michalin/ZX2020/Schematic/TMS9918-2.kicad_sch

## KiCad design Schematic/TMS9918-2.kicad_sch (2022-06-24)

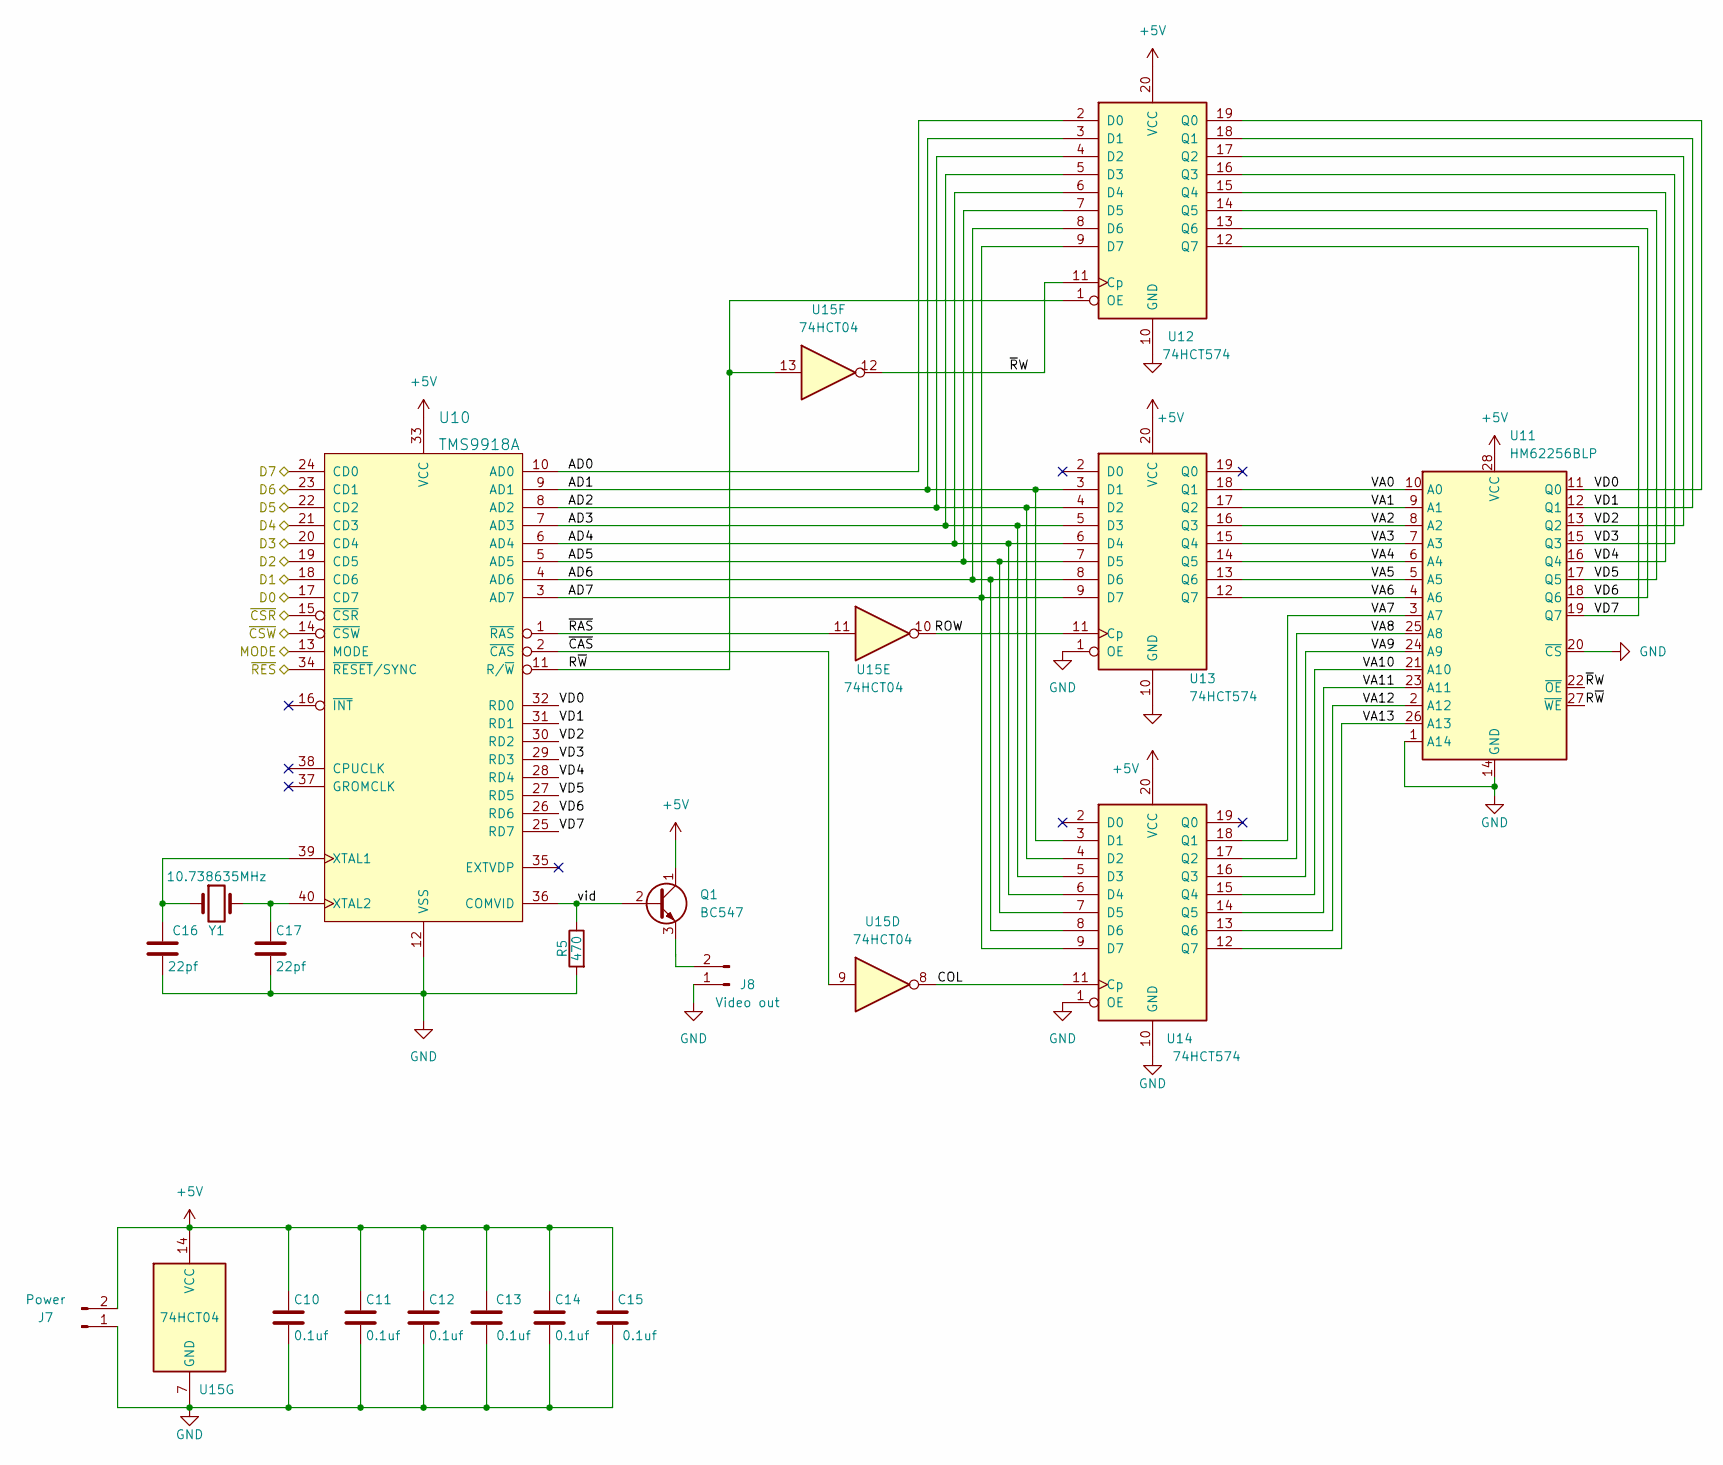
[picture p3: schematic TMS9918-2.kicad_sch]

Parts:
C10, C11, C12, C13, C14, C15: 0.1uf; C_Disc_D3.0mm_W1.6mm_P2.50mm
C16, C17: 22pf; C_Disc_D3.0mm_W1.6mm_P2.50mm
J7: Power; PinHeader_1x02_P2.54mm_Vertical
J8: Video out; PinHeader_1x02_P2.54mm_Horizontal
Q1: BC547; TO-92_Inline
R5: 470; R_Axial_DIN0207_L6.3mm_D2.5mm_P7.62mm_Horizontal
U10: TMS9918A; DIP-40_W15.24mm
U11: HM62256BLP; DIP-28_W15.24mm
U12, U13, U14: 74HCT574; DIP-20_W7.62mm_Socket
U15: 74HCT04; DIP-14_W7.62mm_Socket
Y1: 10.738635MHz; Crystal_HC49-4H_Vertical

Connections:
+5V: C10.1, C11.1, C12.1, C13.2, C14.1, C15.1, J7.2, Q1.1 (C), U10.33 (VCC), U11.28 (VCC), U12.20 (VCC), U13.20 (VCC), U14.20 (VCC), U15.14 (VCC)
AD0: U10.10 (AD0), U12.2 (D0)
AD1: U10.9 (AD1), U12.3 (D1), U13.3 (D1), U14.3 (D1)
AD2: U10.8 (AD2), U12.4 (D2), U13.4 (D2), U14.4 (D2)
AD3: U10.7 (AD3), U12.5 (D3), U13.5 (D3), U14.5 (D3)
AD4: U10.6 (AD4), U12.6 (D4), U13.6 (D4), U14.6 (D4)
AD5: U10.5 (AD5), U12.7 (D5), U13.7 (D5), U14.7 (D5)
AD6: U10.4 (AD6), U12.8 (D6), U13.8 (D6), U14.8 (D6)
AD7: U10.3 (AD7), U12.9 (D7), U13.9 (D7), U14.9 (D7)
COL: U14.11 (Cp), U15.8
D0: U10.17 (CD7)
D1: U10.18 (CD6)
D2: U10.19 (CD5)
D3: U10.20 (CD4)
D4: U10.21 (CD3)
D5: U10.22 (CD2)
D6: U10.23 (CD1)
D7: U10.24 (CD0)
GND: C10.2, C11.2, C12.2, C13.1, C14.2, C15.2, C16.2, C17.2, J7.1, J8.1, R5.2, U10.12 (VSS), U11.1 (A14), U11.14 (GND), U11.20 (~CS), U12.10 (GND), U13.1 (OE), U13.10 (GND), U14.1 (OE), U14.10 (GND), U15.7 (GND)
MODE: U10.13 (MODE)
unnamed: C16.1, U10.39 (XTAL1), Y1.1
unnamed: C17.1, U10.40 (XTAL2), Y1.2
unnamed: J8.2, Q1.3 (E)
ROW: U13.11 (Cp), U15.10
R~W: U10.11 (R/~W), U11.27 (~WE), U12.1 (OE), U15.13
VA0: U11.10 (A0), U13.18 (Q1)
VA1: U11.9 (A1), U13.17 (Q2)
VA2: U11.8 (A2), U13.16 (Q3)
VA3: U11.7 (A3), U13.15 (Q4)
VA4: U11.6 (A4), U13.14 (Q5)
VA5: U11.5 (A5), U13.13 (Q6)
VA6: U11.4 (A6), U13.12 (Q7)
VA7: U11.3 (A7), U14.18 (Q1)
VA8: U11.25 (A8), U14.17 (Q2)
VA9: U11.24 (A9), U14.16 (Q3)
VA10: U11.21 (A10), U14.15 (Q4)
VA11: U11.23 (A11), U14.14 (Q5)
VA12: U11.2 (A12), U14.13 (Q6)
VA13: U11.26 (A13), U14.12 (Q7)
VD0: U10.32 (RD0), U11.11 (Q0), U12.19 (Q0)
VD1: U10.31 (RD1), U11.12 (Q1), U12.18 (Q1)
VD2: U10.30 (RD2), U11.13 (Q2), U12.17 (Q2)
VD3: U10.29 (RD3), U11.15 (Q3), U12.16 (Q3)
VD4: U10.28 (RD4), U11.16 (Q4), U12.15 (Q4)
VD5: U10.27 (RD5), U11.17 (Q5), U12.14 (Q5)
VD6: U10.26 (RD6), U11.18 (Q6), U12.13 (Q6)
VD7: U10.25 (RD7), U11.19 (Q7), U12.12 (Q7)
vid: Q1.2 (B), R5.1, U10.36 (COMVID)
~CAS: U10.2 (~CAS), U15.9
~CSR: U10.15 (~CSR)
~CSW: U10.14 (~CSW)
~RAS: U10.1 (~RAS), U15.11
~RES: U10.34 (~RESET/SYNC)
~RW: U11.22 (~OE), U12.11 (Cp), U15.12
