michalin/ZX2020/Schematic/zx2020.kicad_sch

## KiCad design Schematic/zx2020.kicad_sch (2022-06-24)

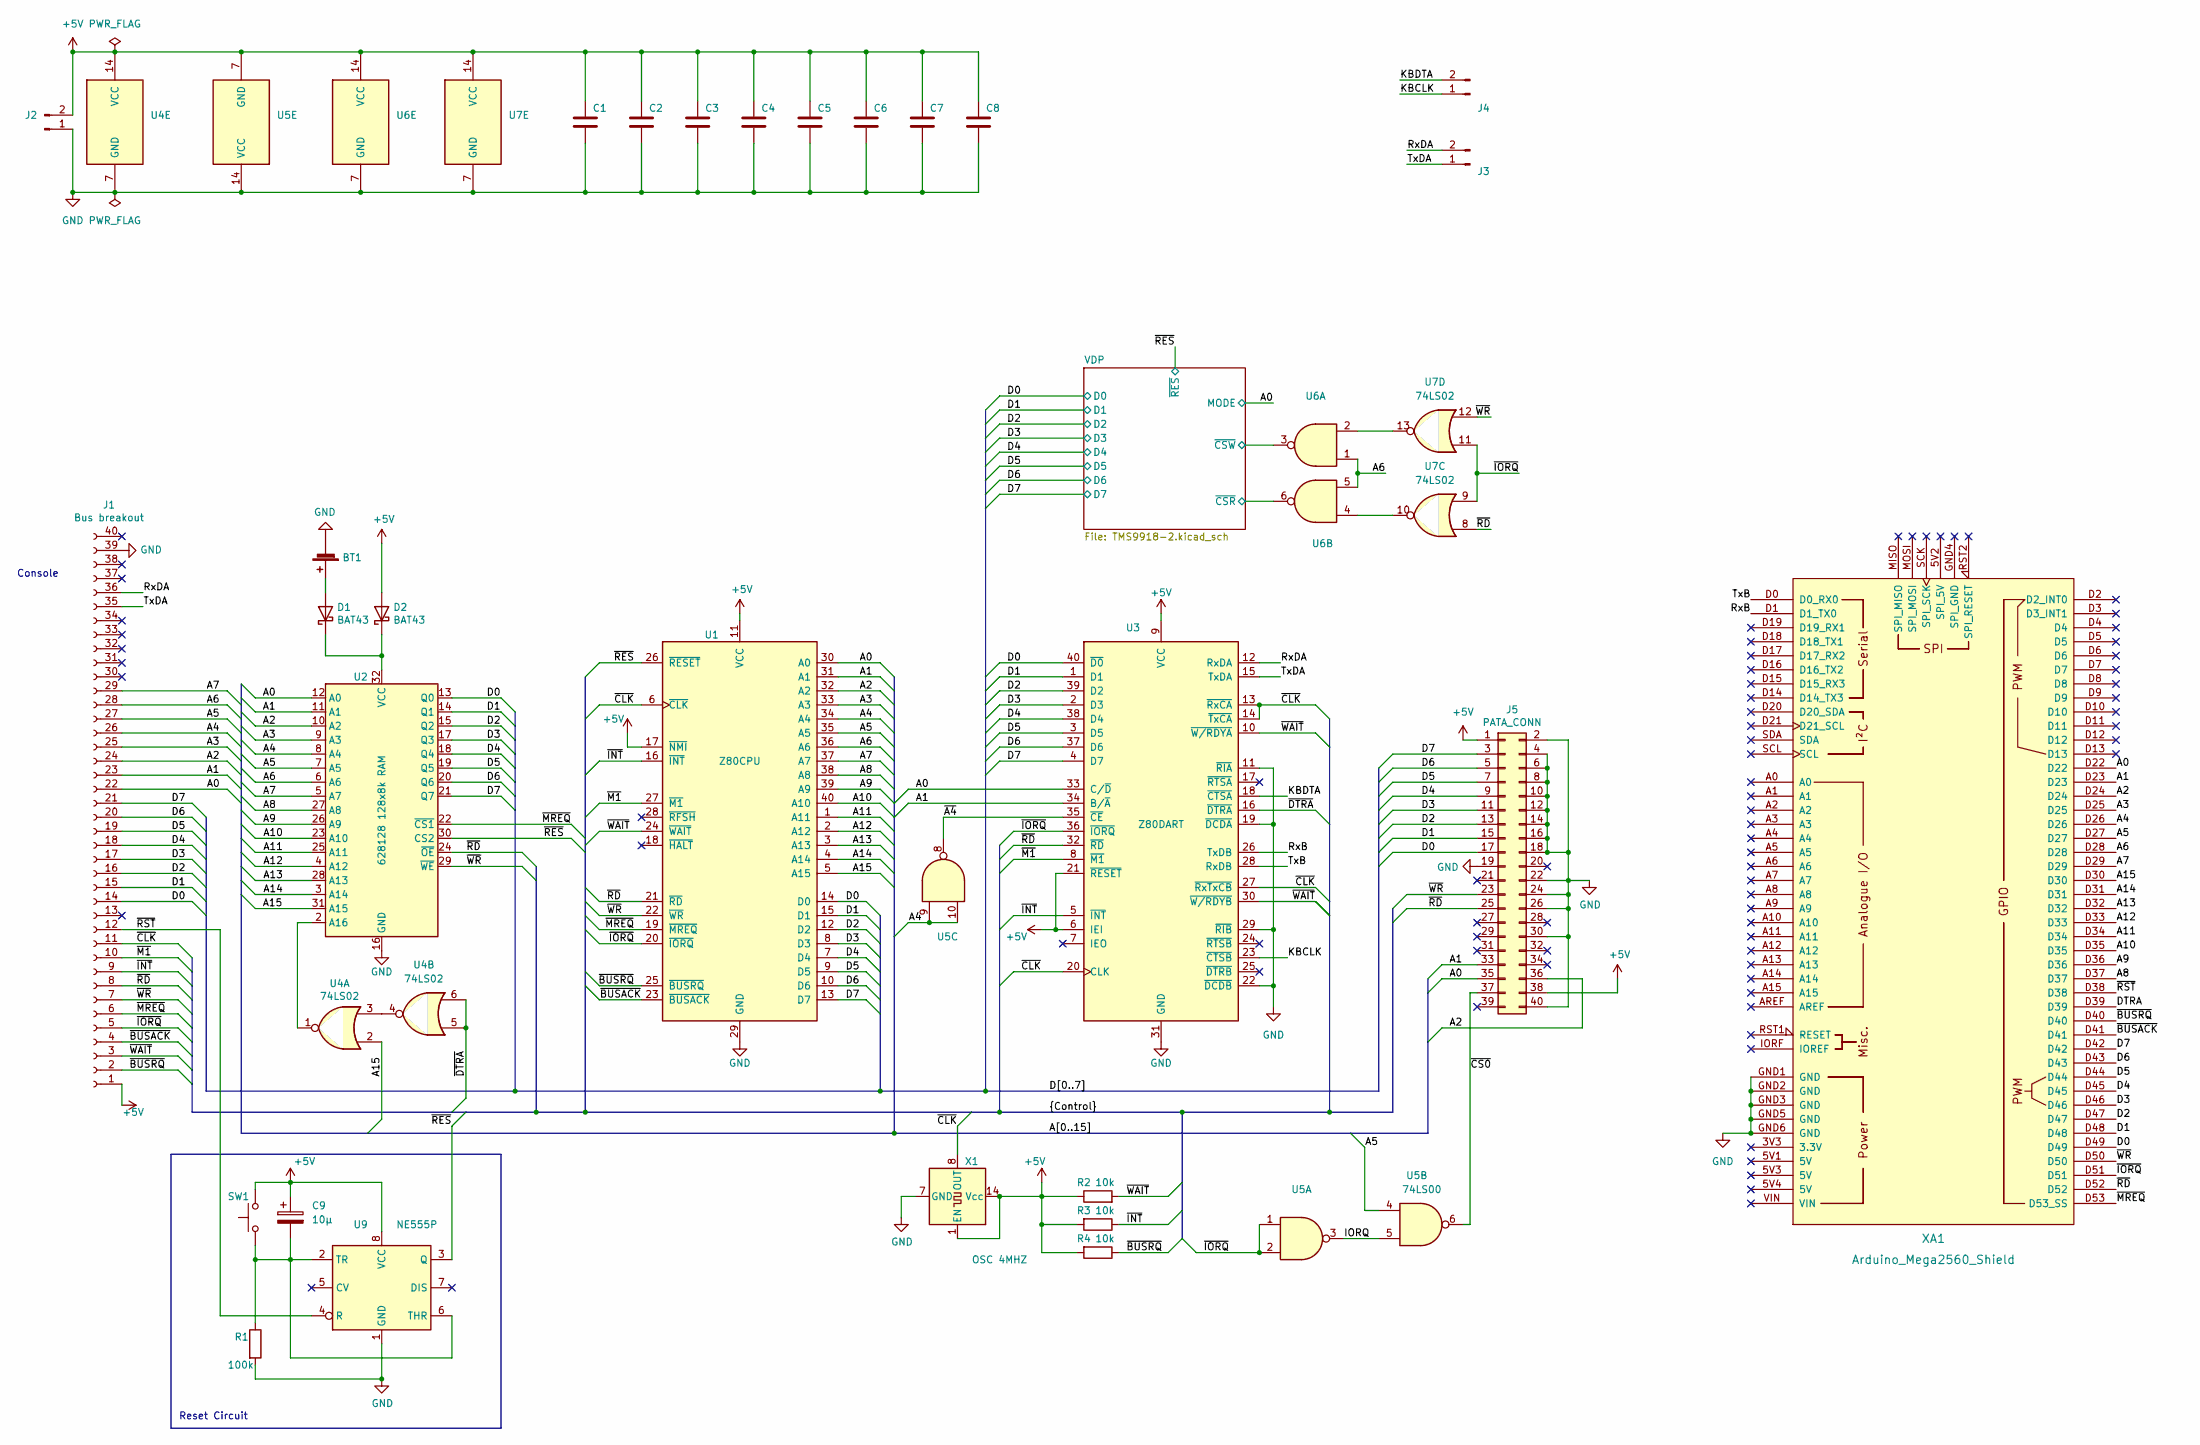
[picture p4: schematic zx2020.kicad_sch]

Parts:
BT1: Battery_Cell
C1, C2, C3, C4, C5, C6, C7, C8: (no value)
C9: 10µ
D1, D2: BAT43; D_DO-35_SOD27_P7.62mm_Horizontal
J1: Bus breakout; PinHeader_1x39_P2.54mm_Vertical
J2, J3, J4: (no value)
J5: PATA_CONN; PinHeader_2x20_P2.54mm_Horizontal
R1: 100k
R2, R3, R4: 10k
SW1: (no value)
U1: Z80CPU; DIP-40_W15.24mm
U2: 628128 128x8k RAM; DIP-32_W15.24mm
U3: Z80DART; DIP-40_W15.24mm
U4: 74LS02; DIP-14_W7.62mm
U5: 74LS00
U6, U7: (no value)
U9: NE555P; DIP-8_W7.62mm
X1: OSC 4MHZ; Oscillator_DIP-14
XA1: Arduino_Mega2560_Shield

Connections:
+5V: C1.1, C2.1, C3.1, C4.1, C5.1, C6.1, C7.1, C8.1, C9.1, D2.2 (A), J1.1, J2.2, J5.1, J5.38, R2.1, R3.2, R4.2, SW1.2, U1.11 (VCC), U1.17 (~NMI), U3.6 (IEI), U3.9 (VCC), U3.21 (~RESET), U4.14 (VCC), U5.7 (GND), U6.14 (VCC), U7.14 (VCC), U9.8 (VCC), X1.1 (EN), X1.14 (Vcc)
A0: J1.22, J5.35, U1.30 (A0), U2.12 (A0), U3.33 (C/~D), XA1.D22
A1: J1.23, J5.33, U1.31 (A1), U2.11 (A1), U3.34 (B/~A), XA1.D23
A2: J1.24, J5.36, U1.32 (A2), U2.10 (A2), XA1.D24
A3: J1.25, U1.33 (A3), U2.9 (A3), XA1.D25
A4: J1.26, U1.34 (A4), U2.8 (A4), U5.9, U5.10, XA1.D26
A5: J1.27, U1.35 (A5), U2.7 (A5), U5.4, XA1.D27
A6: J1.28, U1.36 (A6), U2.6 (A6), U6.1, U6.5, XA1.D28
A7: J1.29, U1.37 (A7), U2.5 (A7), XA1.D29
A8: U1.38 (A8), U2.27 (A8), XA1.D37
A9: U1.39 (A9), U2.26 (A9), XA1.D36
A10: U1.40 (A10), U2.23 (A10), XA1.D35
A11: U1.1 (A11), U2.25 (A11), XA1.D34
A12: U1.2 (A12), U2.4 (A12), XA1.D33
A13: U1.3 (A13), U2.28 (A13), XA1.D32
A14: U1.4 (A14), U2.3 (A14), XA1.D31
A15: U1.5 (A15), U2.31 (A15), U4.2, XA1.D30
D0: J1.14, J5.17, U1.14 (D0), U2.13 (Q0), U3.40 (~D0), XA1.D49
D1: J1.15, J5.15, U1.15 (D1), U2.14 (Q1), U3.1 (D1), XA1.D48
D2: J1.16, J5.13, U1.12 (D2), U2.15 (Q2), U3.39 (D2), XA1.D47
D3: J1.17, J5.11, U1.8 (D3), U2.17 (Q3), U3.2 (D3), XA1.D46
D4: J1.18, J5.9, U1.7 (D4), U2.18 (Q4), U3.38 (D4), XA1.D45
D5: J1.19, J5.7, U1.9 (D5), U2.19 (Q5), U3.3 (D5), XA1.D44
D6: J1.20, J5.5, U1.10 (D6), U2.20 (Q6), U3.37 (D6), XA1.D43
D7: J1.21, J5.3, U1.13 (D7), U2.21 (Q7), U3.4 (D7), XA1.D42
DTRA: XA1.D39
GND: BT1.2 (-), C1.2, C2.2, C3.2, C4.2, C5.2, C6.2, C7.2, C8.2, J1.39, J2.1, J5.2, J5.4, J5.6, J5.8, J5.10, J5.12, J5.14, J5.16, J5.18, J5.19, J5.22, J5.24, J5.26, J5.30, J5.40, R1.2, U1.29 (GND), U2.16 (GND), U3.11 (~RIA), U3.19 (~DCDA), U3.22 (~DCDB), U3.29 (~RIB), U3.31 (GND), U4.7 (GND), U5.14 (VCC), U6.7 (GND), U7.7 (GND), U9.1 (GND), X1.7 (GND), XA1.GND1 (GND), XA1.GND2 (GND), XA1.GND3 (GND), XA1.GND5 (GND), XA1.GND6 (GND)
IORQ: U5.3, U5.5
KBCLK: J4.1, U3.23 (~CTSB)
KBDTA: J4.2, U3.18 (~CTSA)
unnamed: BT1.1 (+), D1.2 (A)
unnamed: C9.2, R1.1, SW1.1, U9.2 (TR), U9.6 (THR)
unnamed: D1.1 (K), D2.1 (K), U2.32 (VCC)
unnamed: U2.2 (A16), U4.1
unnamed: U4.3, U4.4
unnamed: U6.2, U7.13
unnamed: U6.4, U7.10
RxB: U3.26 (TxDB), XA1.D1 (D1_TX0)
RxDA: J1.36, J3.2, U3.12 (RxDA)
TxB: U3.28 (RxDB), XA1.D0 (D0_RX0)
TxDA: J1.35, J3.1, U3.15 (TxDA)
~A4: U3.35 (~CE), U5.8
~BUSACK: J1.4, U1.23 (~BUSACK), XA1.D41
~BUSRQ: J1.2, R4.1, U1.25 (~BUSRQ), XA1.D40
~CLK: J1.11, U1.6 (~CLK), U3.13 (~RxCA), U3.14 (~TxCA), U3.20 (CLK), U3.27 (~RxTxCB), X1.8 (OUT)
~CS0: J5.37, U5.6
~CSR: U6.6
~CSW: U6.3
~DTRA: U3.16 (~DTRA), U4.5, U4.6
~INT: J1.9, R3.1, U1.16 (~INT), U3.5 (~INT)
~IORQ: J1.5, U1.20 (~IORQ), U3.36 (~IORQ), U5.1, U5.2, U7.9, U7.11, XA1.D51
~M1: J1.10, U1.27 (~M1), U3.8 (~M1)
~MREQ: J1.6, U1.19 (~MREQ), U2.22 (~CS1), XA1.D53 (D53_SS)
~RD: J1.8, J5.25, U1.21 (~RD), U2.24 (~OE), U3.32 (~RD), U7.8, XA1.D52
~RES: U1.26 (~RESET), U2.30 (CS2), U9.3 (Q)
~RST: J1.12, U9.4 (R), XA1.D38
~WAIT: J1.3, R2.2, U1.24 (~WAIT), U3.10 (~W/RDYA), U3.30 (~W/RDYB)
~WR: J1.7, J5.23, U1.22 (~WR), U2.29 (~WE), U7.12, XA1.D50

Notes on the sheet:
Console
Reset Circuit
